Phisik/Peristaltic-Pump/stl/case-with-support.stl

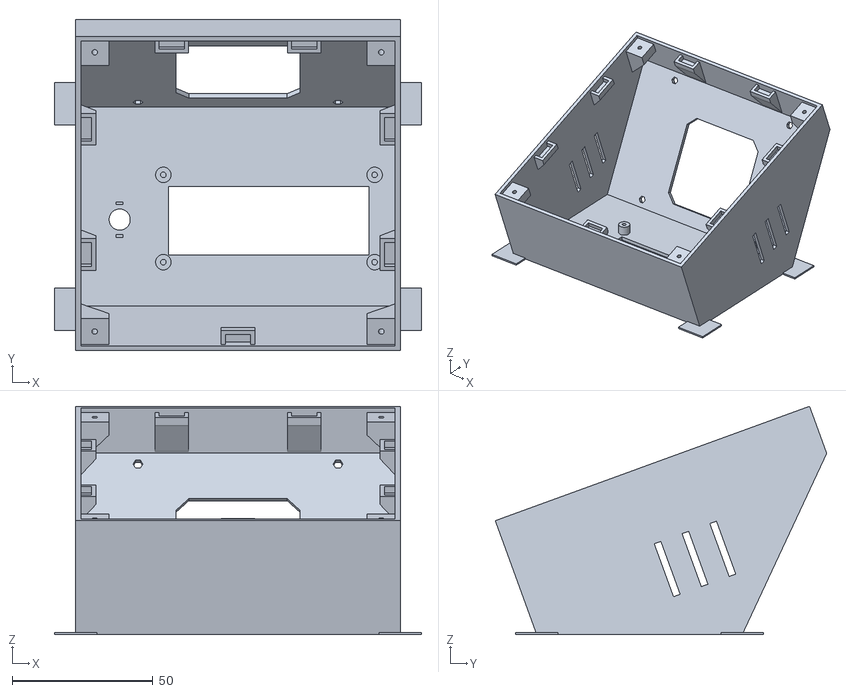
[picture p16: CAD file, 2019-03-04]
stl/case-with-support.stl
130.3 x 117.7 x 81.1
