Phisik/Peristaltic-Pump/stl/pump-stator-support.stl

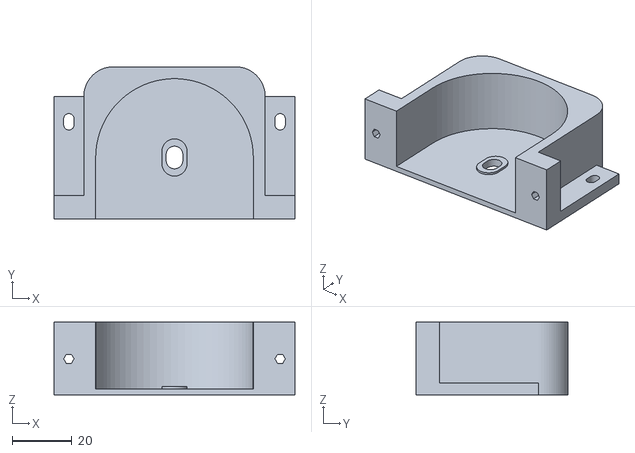
[picture p17: CAD file, 2019-03-04]
stl/pump-stator-support.stl
81.0 x 51.2 x 24.4
