Phisik/Peristaltic-Pump/stl/hose-joiner.stl

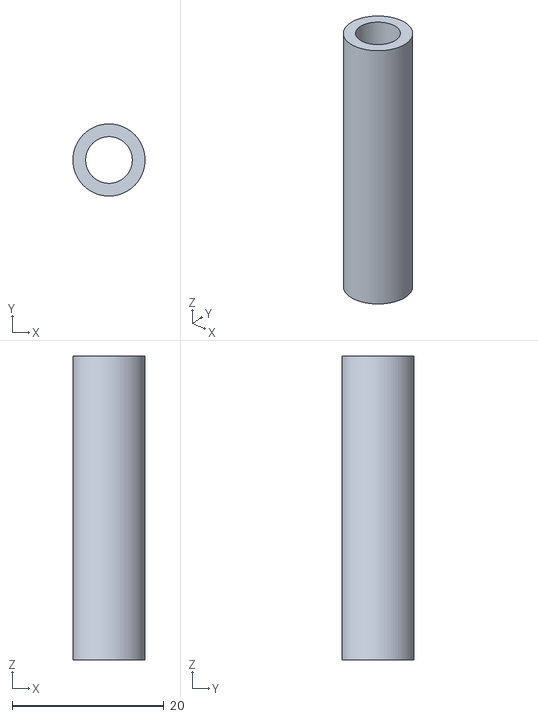
[picture p18: CAD file, 2019-03-04]
stl/hose-joiner.stl
9.50 x 9.50 x 40.0
